chayanforyou/Standalone-Arduino-AVR-ISP-programmer/Others/Tutorial/Step  (3).png

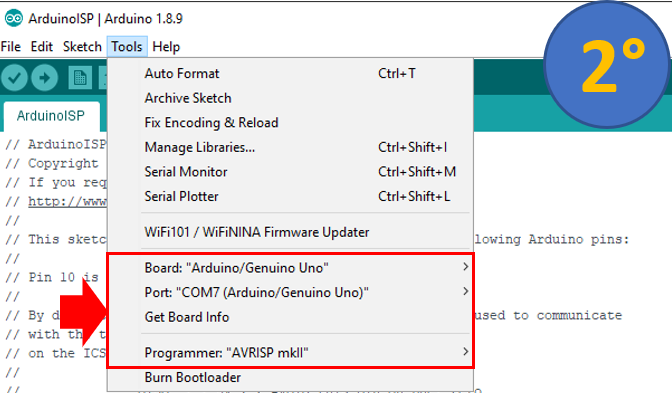
Others/Tutorial/Step (3).png
