chayanforyou/Standalone-Arduino-AVR-ISP-programmer/Others/Tutorial/Step  (4).png

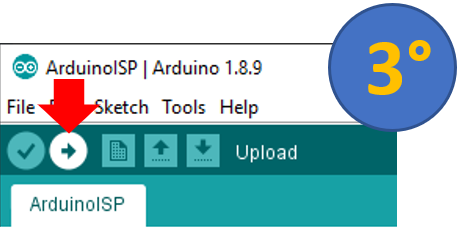
Others/Tutorial/Step (4).png
