chayanforyou/Standalone-Arduino-AVR-ISP-programmer/Others/Tutorial/Step  (8).png

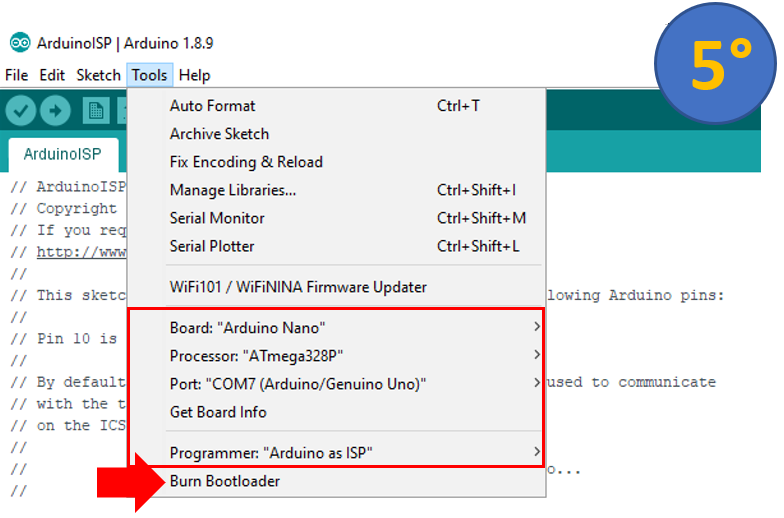
Others/Tutorial/Step (8).png
