chayanforyou/Standalone-Arduino-AVR-ISP-programmer/Others/Tutorial/Step  (11).png

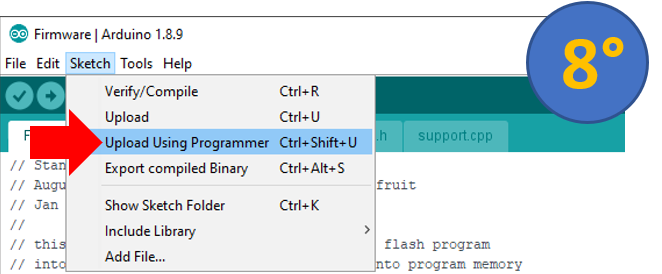
Others/Tutorial/Step (11).png
